K1riT0N/mobile-robot-competition/Reports/ROBOTIC COMPETITION REPORT.pdf

### KING MONGKUT’S INSTITUTE OF TECHNOLOGY LATKRABANG

### SCHOOL OF ENGINEERING

### ROBOTIC & AI ENGINEERING

### GROUP OF (RAI 1, RAI 2, HUACHIEW)

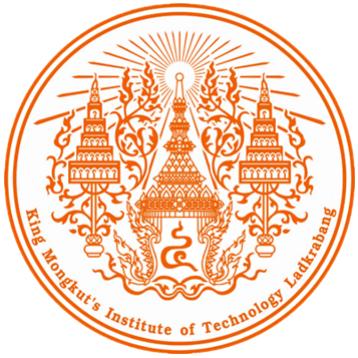
[picture p18: figure]

### ROBOTICS COMPETITION REPORT

INSTRUCTED BY: DR. POOM KONGHUAYROB

NAME: JAIJAI, NUUN, TITLE

GROUP NO: 03

DATE OF SUB.: 10/11/2568

### PURPOSE

- To practice coding for controlling real hardware such as motors, servos, and sensors.
- To create a function robots in both autonomous and manual control systems
- To develop 3D design and programming skill
- To apply physics principles to development and improvement of robotics systems for future innovation.

## AUTONOMOUS ROBOT

### COMPONENT LIST

- Arduino UNO
Parameter | Specification
microcontroller | ATmega328P
USB Controller | ATmega16U2
Operating Voltage | 5 V
Input Voltage | 7 - 12 V
Difital I/O Pins | 14 (6 PWM)
Communication | UART, I²C, SPI
Dimensions | 68.6 x 53.4 mm
Weight | 25 g

- TT DC Motor Dual-Shaft
Parameter | Specification
Gear Reduction Ratio | 1:48
Rated Voltage | 3 – 6 V
No-load Speed | ≈200 RPM at 6V
No-load Current | ≈150 mA at 6V
Stall Torque | ≈0.8 kg cm at 6V
Stall Current | ≈700 mA
Shaft Type | Double D-shaped output shaft
Gearbox Material | Plastic
Dimensions | ≈70 × 22 × 18 mm
Weight | ≈30 – 50 g
Power | ≈0.9 W
- SG90 Servo Motor 9g
Parameter | Specification
Operating Voltage | 4.8 - 6 V DC
Operating Current (No Load) | ~100 mA
Stall Current | ~680 mA
Torque | 1.8 kg cm at 4.8 V
Speed | 0.1 s/60° at 4.8 V
Rotation Angle | ~180°
Weight | 9 g

- Gyro Sensor MPU6050 GY-521
Parameter | Specification
Supply Voltage | 3 - 5 V DC
Gyro Range | ±250, ±500, ±1000, ±2000 °/s
Accelerometer Range | ±2g, ±4g, ±8g, ±16g
Operating Current | ~3.9 mA
Communication Speed | 400 kHz I²C
- L298N
Parameter | Specification
Motor Supply Voltage | 5 - 35 V DC
Logic Supply Voltage | 5 V
Continuous Output Current | 2 A per channel
Channels | 2 DC motors
Control Inputs | IN1, IN2, IN3, IN4
PWM Control | ENA, ENB
Peak Output Current | 3 A per channel
Thermal Shutdown | Build in

### ASSEMBLY DESIGN

### 1.1 Cube Collecting Mechanism

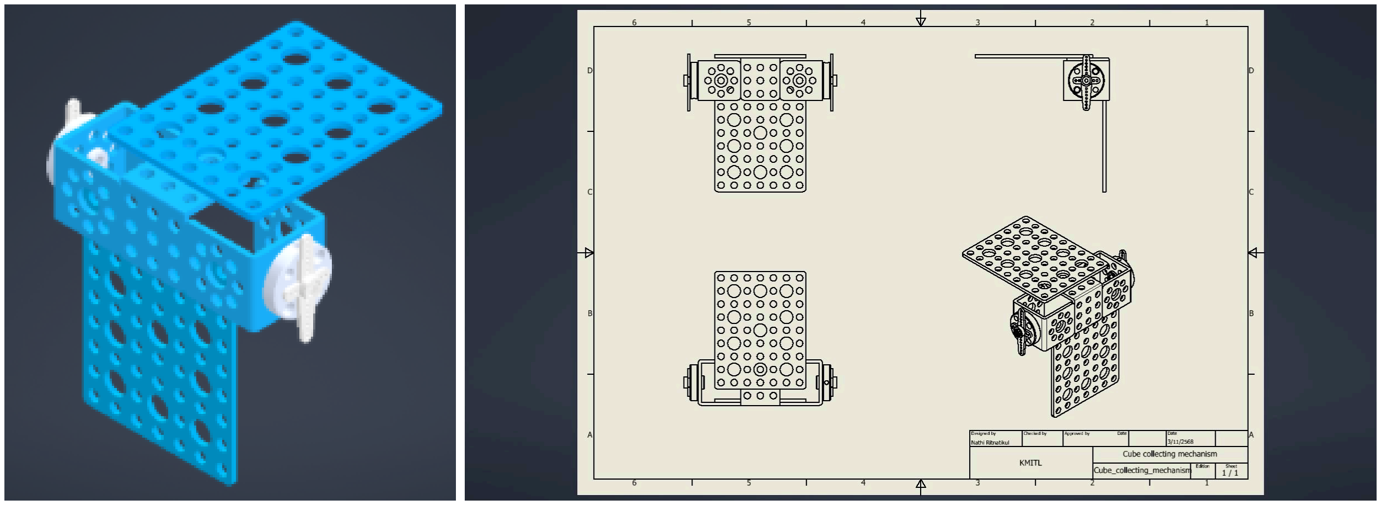
[picture p19: figure]
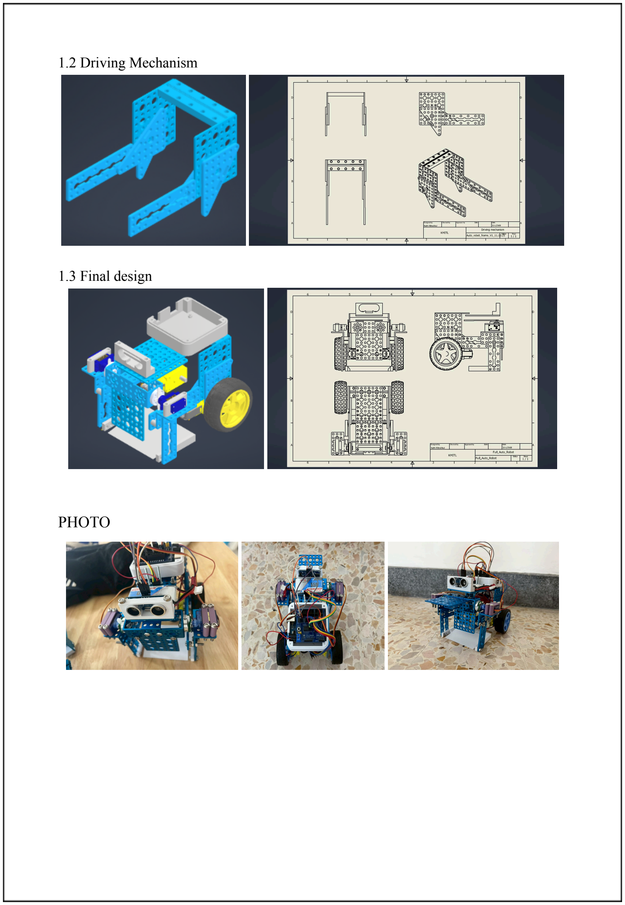
[picture p20: page 5]

### 1.2 Driving Mechanism

### 1.3 Final design

### PHOTO

### ELECTRICAL DIAGRAM

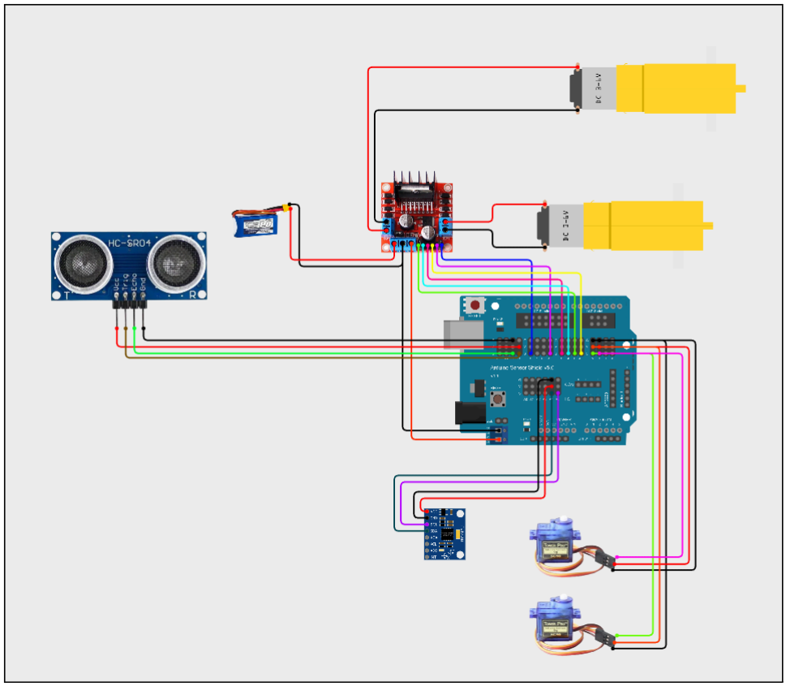
[picture p21: figure]

### CODING

- FLOWCHART

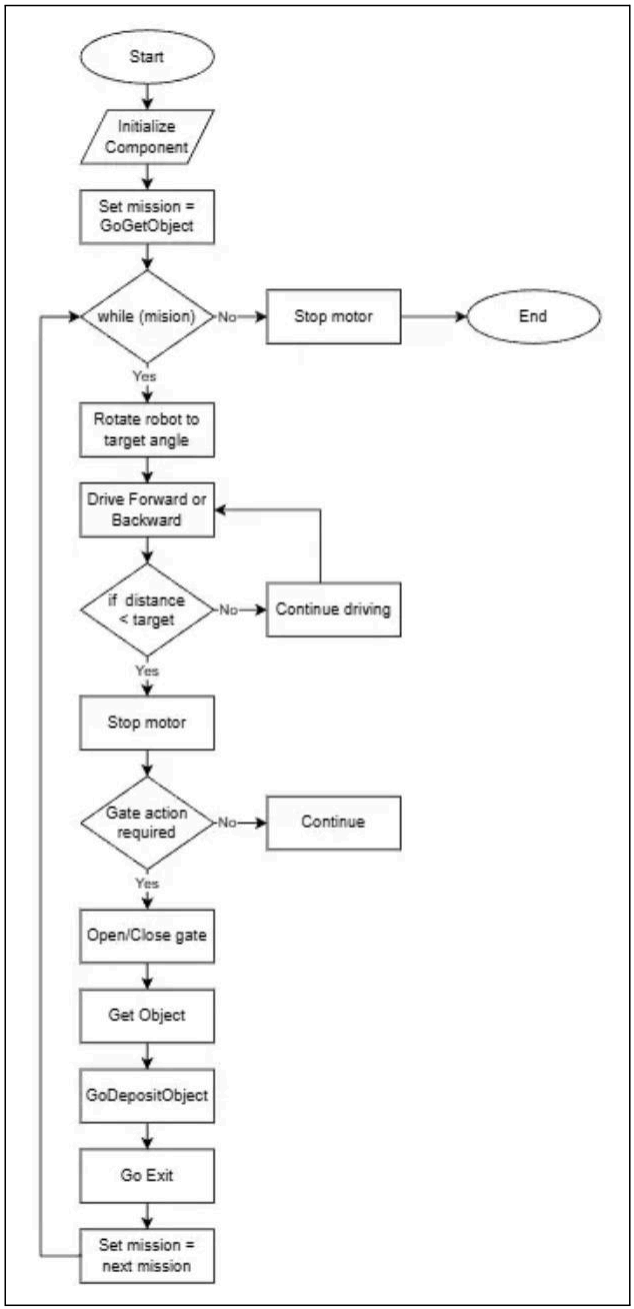
[picture p22: figure]

- FULL CODE AND EXPLANATION

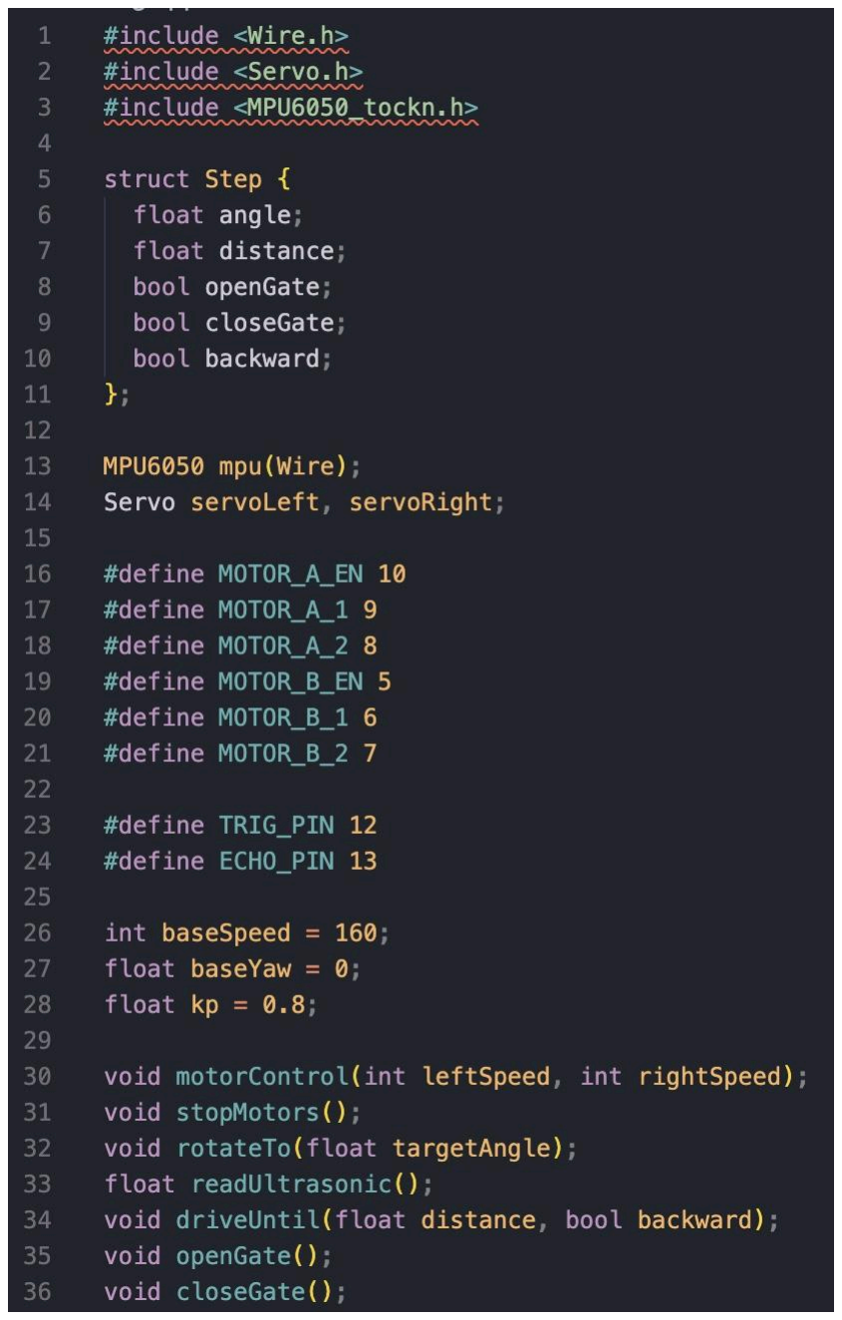
[picture p23: figure]

This part of the code sets up the fundamental structure, hardware definitions, and function declarations for an Arduino robot project that uses sensors and servos for motion and control. It begins by including three essential libraries: Wire.hfor I2C communication, Servo.h for controlling servo motors, and MPU6050_tockn.h for reading data from the MPU6050 gyro sensor. A custom structure named Step is then defined to store parameters for each robot movement, including turning angle, travel distance, and Boolean flags for actions such as openGate, closeGate, and backward. Next, objects for the MPU6050 sensor (mpu) and two servo motors (servoLeft and servoRight) are created. The motor pins for both left and right motors (MOTOR_A and MOTOR_B) are defined, along with the TRIG and ECHO pins used by the ultrasonic sensor for distance measurement. Several control constants are also initialized: baseSpeed (the normal motor speed), baseYaw (the initial orientation angle), and kp (the proportional control gain for rotation). Finally, a set of function prototypes is declared for key robot operations such as controlling motor speed, stopping, rotating to a specific angle, reading distance, driving a set distance, and opening or closing the servo-controlled gate which will be implemented later in the code.

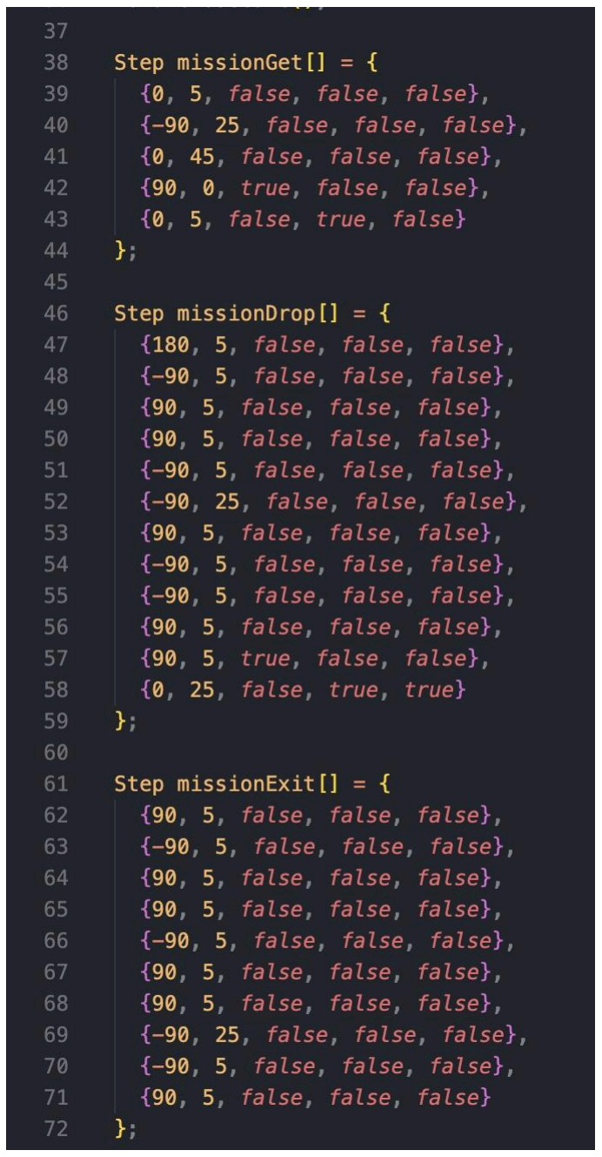
[picture p24: figure]

This section of the code defines three arrays — missionGet, missionDrop, and missionExit — each representing a different sequence of movement and action steps for the robot to perform during its operation. Each array is composed of elements based on the previously defined Step structure, where each step includes five parameters: the rotation angle, travel distance, and three Boolean flags (openGate, closeGate, backward) that specify additional actions.

missionGet describes the robot’s path for approaching and collecting an object. It includes commands to move forward, turn at specific angles (e.g., -90° or 90°), open the servo gate to collect the object, and then close it after pickup.

missionDrop outlines the robot’s path to transport and release the object. It involves multiple turns and straight movements to navigate toward the drop-off location, execute gate-opening actions to release the item, and finally close the gate while possibly reversing.

missionExit defines the route for the robot to leave the drop zone and return or exit the mission area, using a sequence of turns and short distance movements similar to the previous missions but without opening or closing the gate.

Overall, these structured arrays act as predefined mission plans, allowing the robot to follow step-by-step instructions autonomously without hardcoding movement logic inside the main loop.

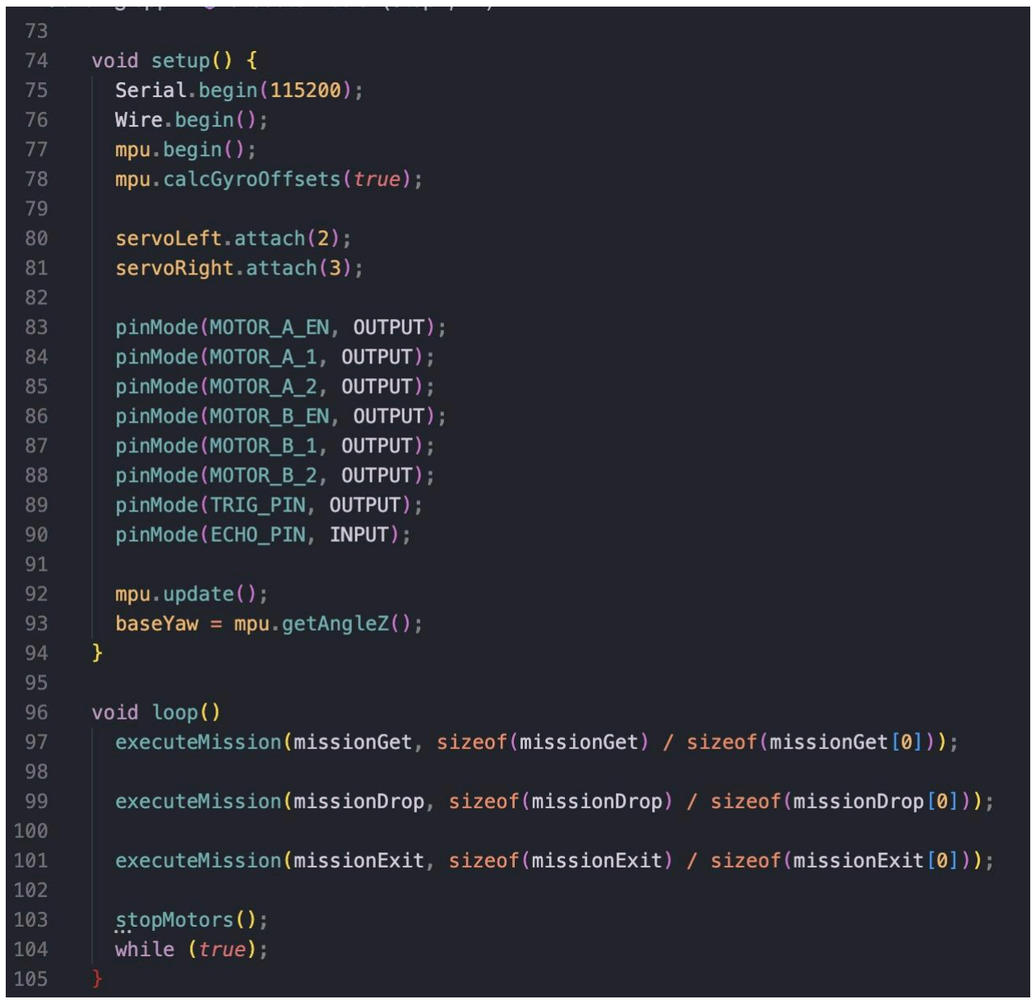
[picture p25: figure]

This part of the code initializes and defines the robot's main operational sequence. The setup() function is run once to prepare the hardware: it starts serial communication and I2C communication for sensors, initializes the MPU-6050 sensor (IMU) and calibrates its gyroscope, attaches the servo motors for mechanical actions, and sets the input/output roles for the DC motor control and ultrasonic sensor pins . It concludes by reading the initial heading from the MPU, storing it as baseYaw for navigation reference. The loop() function then runs the robot's complete mission by sequentially executing three defined phases: missionGet, missionDrop, and missionExit. After completing all three missions, it calls stopMotors() to disable movement and enters an infinite while(true) loop, effectively ending the robot's active program execution.

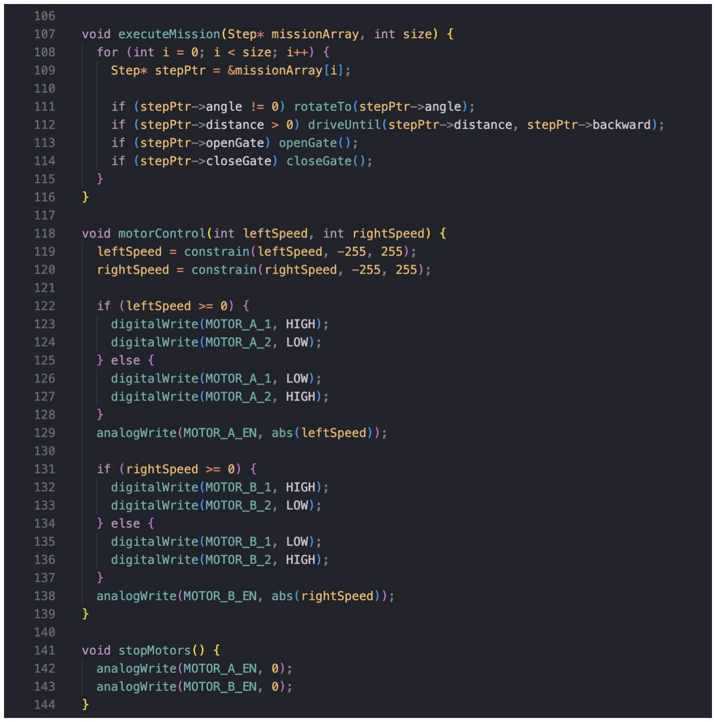
[picture p26: figure]

This segment of code contains the core motion and mission control logic for the robot. The executeMission() function is responsible for iterating through an array of mission steps and calling the appropriate action functions based on the step's data (angle, distance, openGate, or closeGate). The motorControl() function manages the speed and direction of the drive motors: it first ensures the input leftSpeed and rightSpeed values are within the acceptable range (-255 to 255) using constrain(); it then uses digitalWrite() on pins MOTOR_A_1/2 and MOTOR_B_1/2 to set the direction(forward or backward) and employs analogWrite() on the enable pins (MOTOR_A_EN and MOTOR_B_EN) with the absolute speed value to set the motor's velocity using PWM. Finally, the simple stopMotors() function immediately halts both motors by setting the PWM signal on their enable pins to 0.

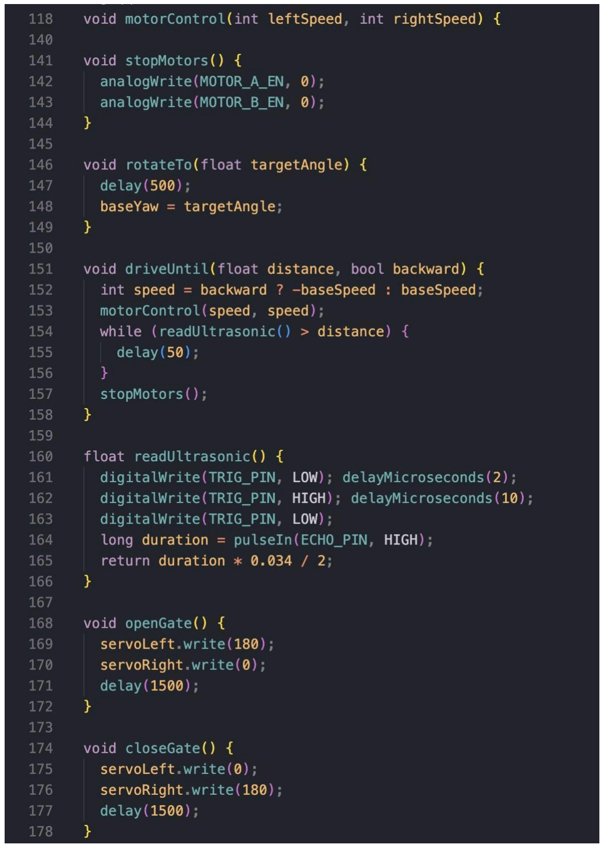
[picture p27: figure]

This section contains the specialized movement and sensing functions of the robot. The readUltrasonic() function measures distance by sending a brief pulse from the TRIG_PIN, waiting for the return echo on the ECHO_PIN , and converting the sound wave's travel time into centimeters. The driveUntil() function moves the robot forward or backward at a defined base speed using motorControl() and continuously checks the distance from the ultrasonic sensor; it stops the motors once the remaining distance is less than the target distance. The rotateTo() function simply sets a new baseYaw reference angle for navigation after a short pause. Lastly, the openGate() and closeGate() functions control the robot's mechanical action by commanding the two servo motors to move to their respective extreme angles (0 or 180 degrees) and pausing briefly to allow the action to complete.

### CODE Explanation

The objective of this project is to design and implement an Arduino-controlled robot that can autonomously navigate a predefined path, perform object collection and drop-off tasks, and finally return to the exit.

The robot uses an ultrasonic distance sensor to detect obstacles, servo motors to operate a gate mechanism, and DC motors to move and rotate according to programmed instructions. At first we were planning on using gyro (MPU6050) but the coding part doesn't work so we use other methods to code without gyro instead.

- Functions : for organized, reusable code blocks.
- Structure (struct) : to store mission step data such as angle, distance, and gate action.
- Array : to hold multiple mission steps for each phase of the route.
- Pointer : to iterate and access mission step data dynamically.
- Loops : to repeatedly execute mission sequences automatically.

Explanation of Main Components

A structure named MissionStep is declared to store

- targetAngle : defines how much the robot should rotate before moving forward
- distance : defines the forward movement distance in centimeters measured by the ultrasonic sensor.
- gateAction : determines whether to open or close the servo gate during that step.

This makes it easy to represent every movement and action as one simple, structured dataobject.

Array and Pointer

The program defines three separate arrays to represent the route phases:

1. getObject[] → path for collecting the object
2. dropObject[] → path for delivering the object
3. exitPath[] → path to return to the exit

Each array contains multiple MissionStep elements describing angles, distances, and gate actions.

A pointer MissionStep* missionPtr is used to access the array dynamically during loop execution:

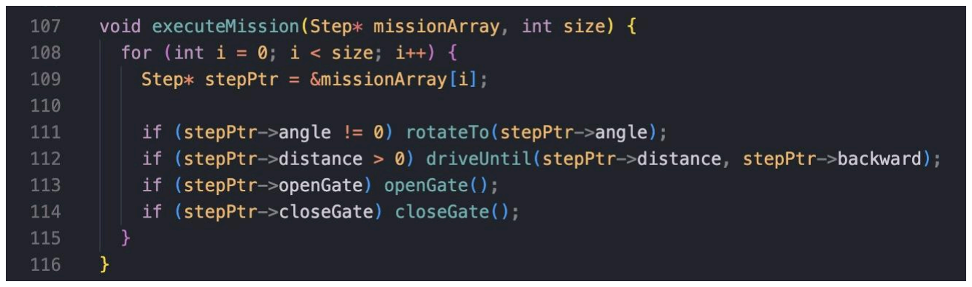
[picture p28: figure]

This loop executes:

Rotation : robot turns to target angle.

Forward movement : continues until ultrasonic sensor reads the specified distance.

Gate control : opens/closes if gateAction = true.

Using for loops reduces code repetition and enables multiple mission sequences to run automatically.

Functions
setupMotors() : Initializes motor driver pins.
driveStraight(int speed) : Moves robot forward at given speed. stopMotors() : Stops both motors.
readUltrasonic() : Reads distance in cm using the ultrasonic sensor. rotateTo(float targetAngle): Simulates rotation to a desired angle. openGate() / closeGate(): Controls servo motors for gate mechanism.

## Control Flow Explanation (Logic)

### Go Get Object

- Robot starts moving forward until the ultrasonic sensor detects an object at 5 cm.
- Turns left 90° and continues 25 cm forward.
- Turns right 90°, moves 45 cm, then right 90° again.
- At this position, the robot opens the gate to collect the object.
- Moves forward 5 cm, then closes the gate.

### Go Drop Object

- Robot turns 180°, retraces its path through a sequence of left and right turns and forward moves (5–25 cm each).
- After reaching the drop location, the robot opens the gate to release the object.
- Moves backward 25 cm, then closes the gate to prepare for exit.

### Go to EXIT

- The robot follows a complex navigation path using multiple 90° turns and 5 cm forward moves.
- Finally stops when it reaches the final exit point, completing the mission.
- Each phase is represented as a series of MissionSteps processed in sequence by the same loop logic — demonstrating modular programming and structural reusability.

## Sensor and Actuator Coordination

The ultrasonic sensor (using TRIG and ECHO pins) constantly measures distance using sound wave reflection.
It controls when the robot should stop moving forward.

The servo motors attached to the gate act as the mechanical arm for grabbing or releasing the object.

DC motors are used for driving and turning, controlled by PWM signals (analogWrite()).

## MANUAL ROBOT

### COMPONENT LIST

- 180 Optical Encoder Motor
Parameter | Specification
Rated voltage | 7.4 V
Gear reduction ratio | 39.6 : 1
No-load current | 240 mA
Load current | ≤ 750 mA
No-load speed | 350 ± 5% RPM
Original motor speed | 14,000 ± 5% RPM
Start torque | 5 kg cm
Rated torque | 0.8 kg cm
Output shaft length | 9 mm
Power | 3.7 W
Encoder rotation angle | 360°
Motor type | DC motor with encoder
Control method | PWM or closed-loop feedback via encoder
- MS-1.5A Servo
Parameter | 4.6 V | 6.0 V | Unit | Tolerance
Running speed (no load) | 0.11 s/60° | 0.10 s/60° | s/60° | ±0.01 s
Operating current (no load) | 270 mA | 380 mA | mA | ±50 mA
Stall torque (locked) | 1.5 kg·cm | 1.8 kg·cm | kg·cm | ±0.30 kg·cm
Stall current (locked) | 1200 mA | 1500 mA | mA | ±50–70 mA
Idle current (when stopped) | 4 mA | 4 mA | mA | ±1 mA
Service life (no load) | >180,000 cycles | >150,000 cycles | cycles | –

- Digital Servo MEDS15
Parameter | Specification
Operating voltage range | 4.8 V to 6.8 V
No-load idle current | 4-5 mA
No-load speed | 62 - 71 RPM (at 6.8V)
Stall torque | 18 - 21.5 kg cm (at 6.8V)
Stall current | 1.5 - 2.2 A (at 5 - 6.8V)
Control signal | PWM (pulse-width modulated)
Rotation Range | 180°
- TT DC Motor Single-Shaft
Parameter | Specification
Gear Reduction Ratio | 1:48
Rated Voltage | 3 – 6 V
No-load Speed | ≈200 RPM at 6V
No-load Current | ≈150 mA at 6V
Stall Torque | ≈0.8 kg cm at 6V
Stall Current | ≈700 mA
Shaft Type | Single D-shaped output shaft
Gearbox Material | Plastic
Dimensions | ≈70 × 22 × 18 mm
Weight | ≈30 – 50 g
Power | ≈0.9 W

- mBot2 Shield
Component | Specification
Main Controller | CyberPi
Processor | ESP32-WROVER-B Dual-Core
Memory | 8 MB Flash, 8 MB PSRAM
Display | 1.44-inch Full-Color TFT
Communication | Wi-Fi 2.4GHz / Bluetooth 5.0
Interface Ports | 1×USB-C, 1×mBuild Port, 1×Extension Port
Power Supply | 3.7V Li-ion Battery (2500 mAh typical)
Operating Voltage | 3.3V Logic Level
Programming | mBlock 5 / Python / Arduino Mode
- Bluetooth Controller
Parameter | Specification
Material | ABS
Bluetooth Version | 4.0
Trasmission Distance | 20 m
Power supply | 5AA batteries

### ASSEMBLY DESIGN

### 1.1 Version 1

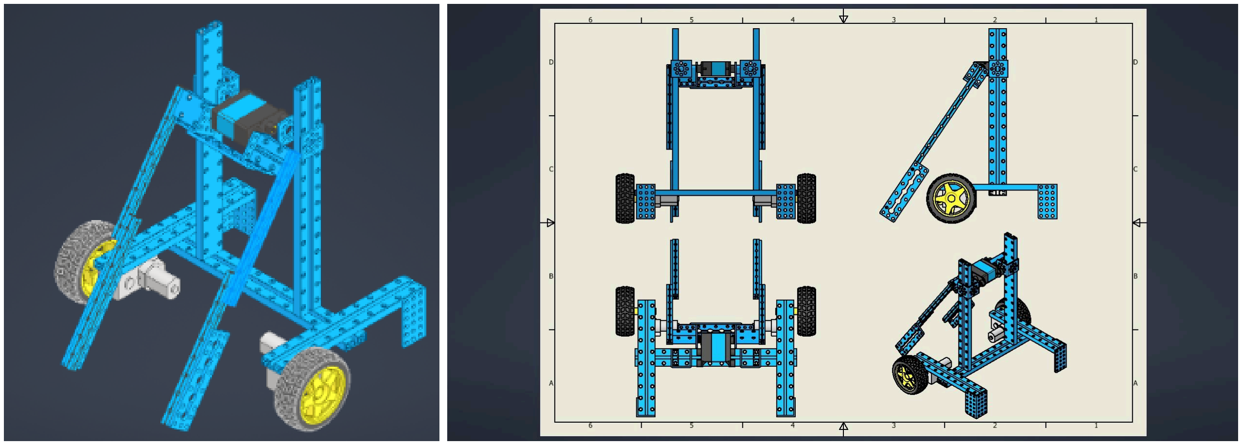
[picture p29: figure]
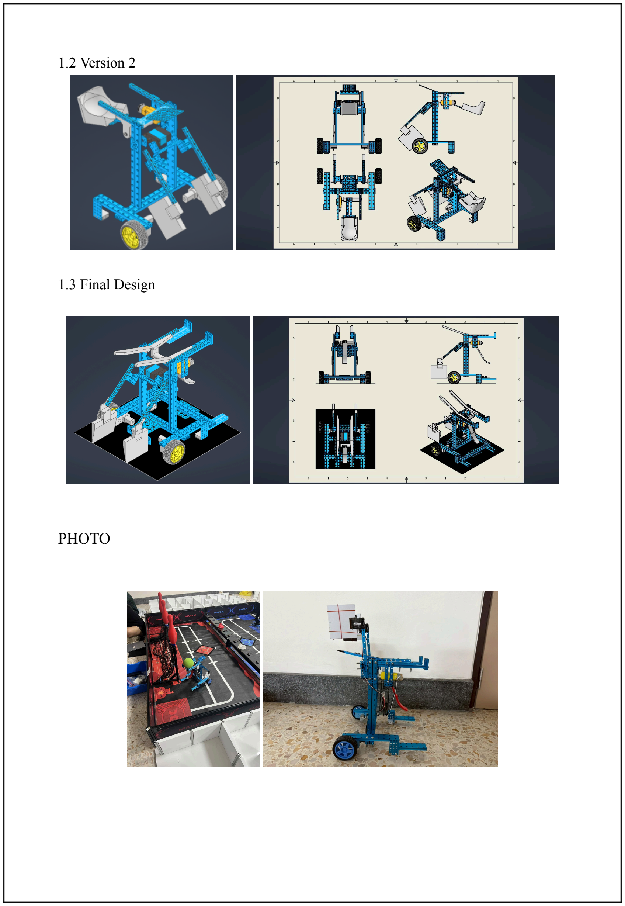
[picture p30: page 19]

### 1.2 Version 2

### 1.3 Final Design

### PHOTO

### ELECTRICAL DIAGRAM

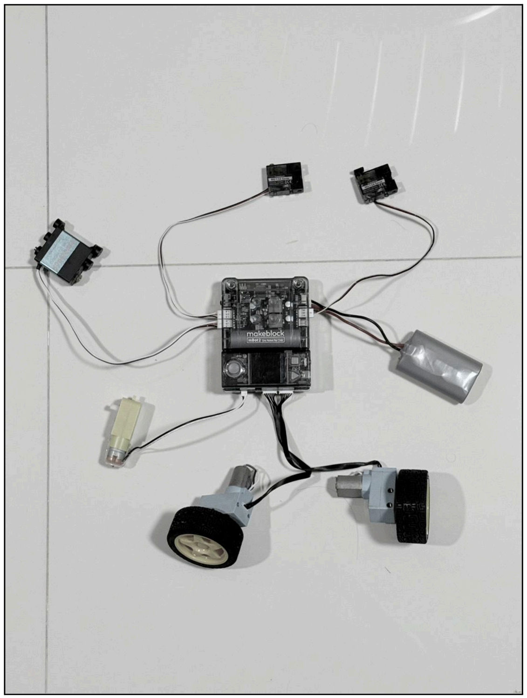
[picture p31: figure]

### CODING

- FLOWCHART

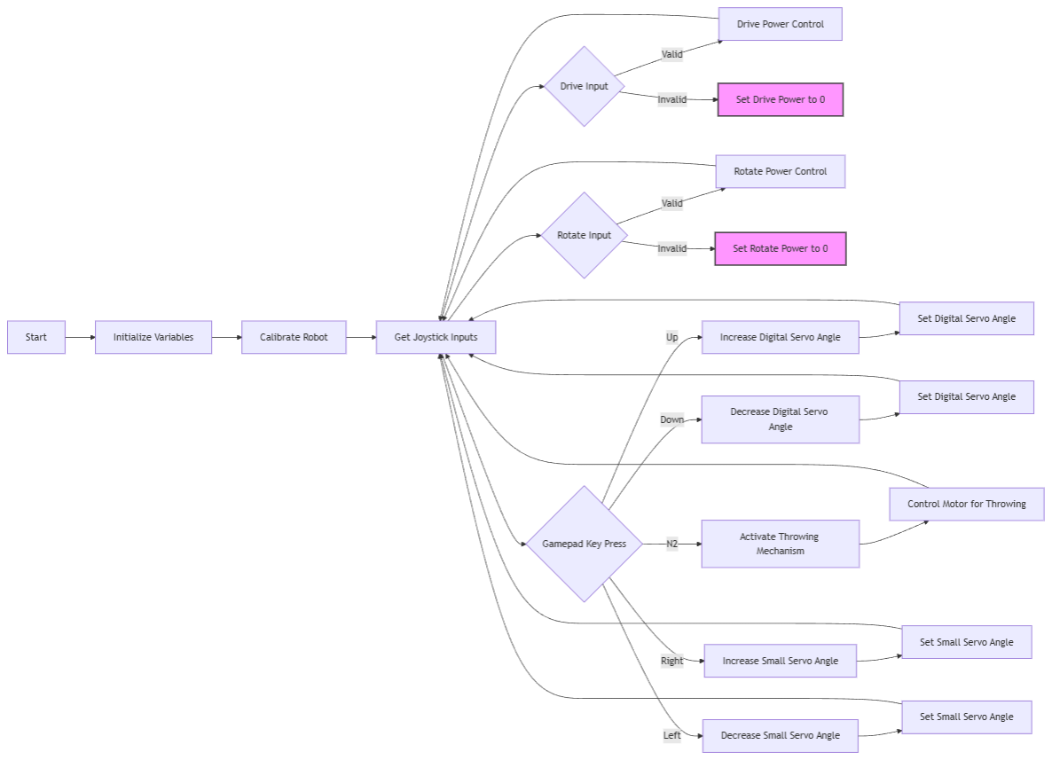
[picture p32: figure]
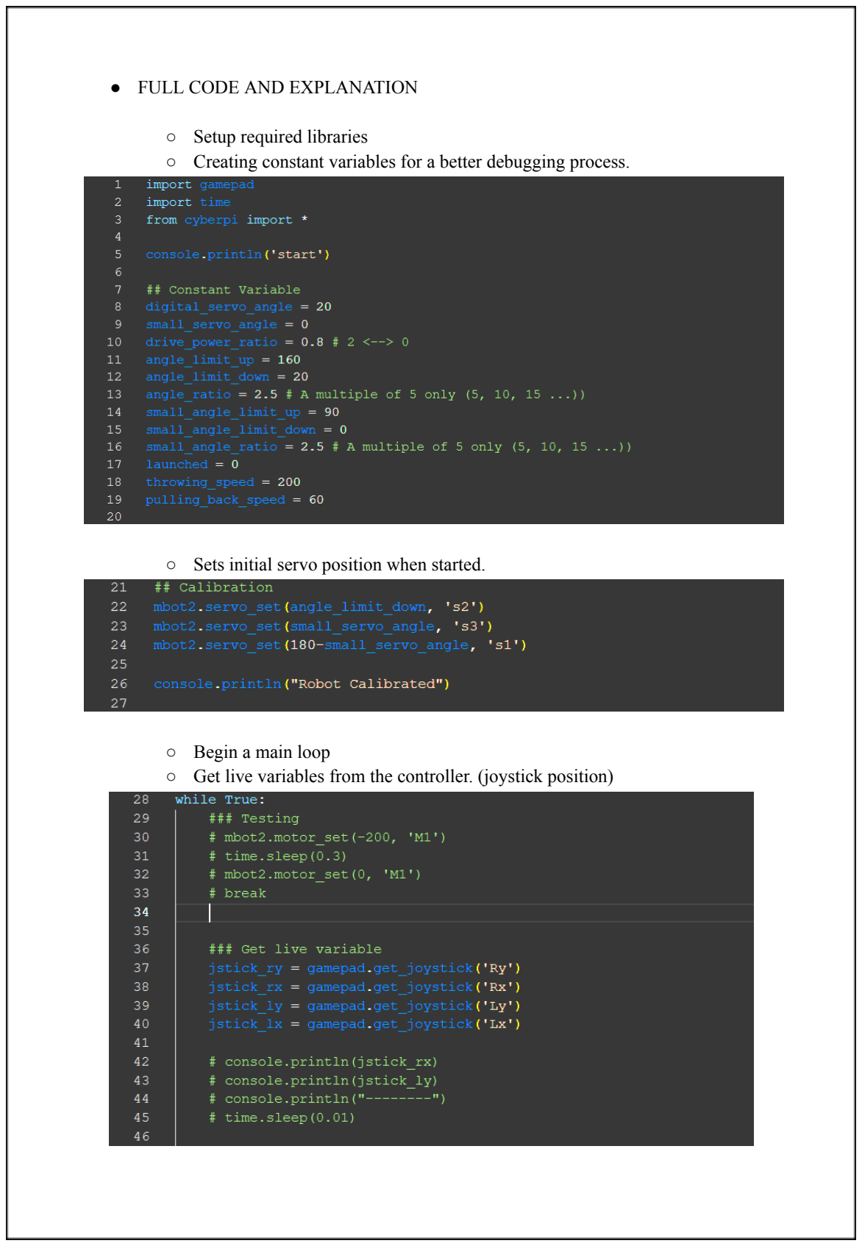
[picture p33: page 22]

- FULL CODE AND EXPLANATION
- Setup required libraries
- Creating constant variables for a better debugging process.
- Sets initial servo position when started.
- Begin a main loop
- Get live variables from the controller. (joystick position)

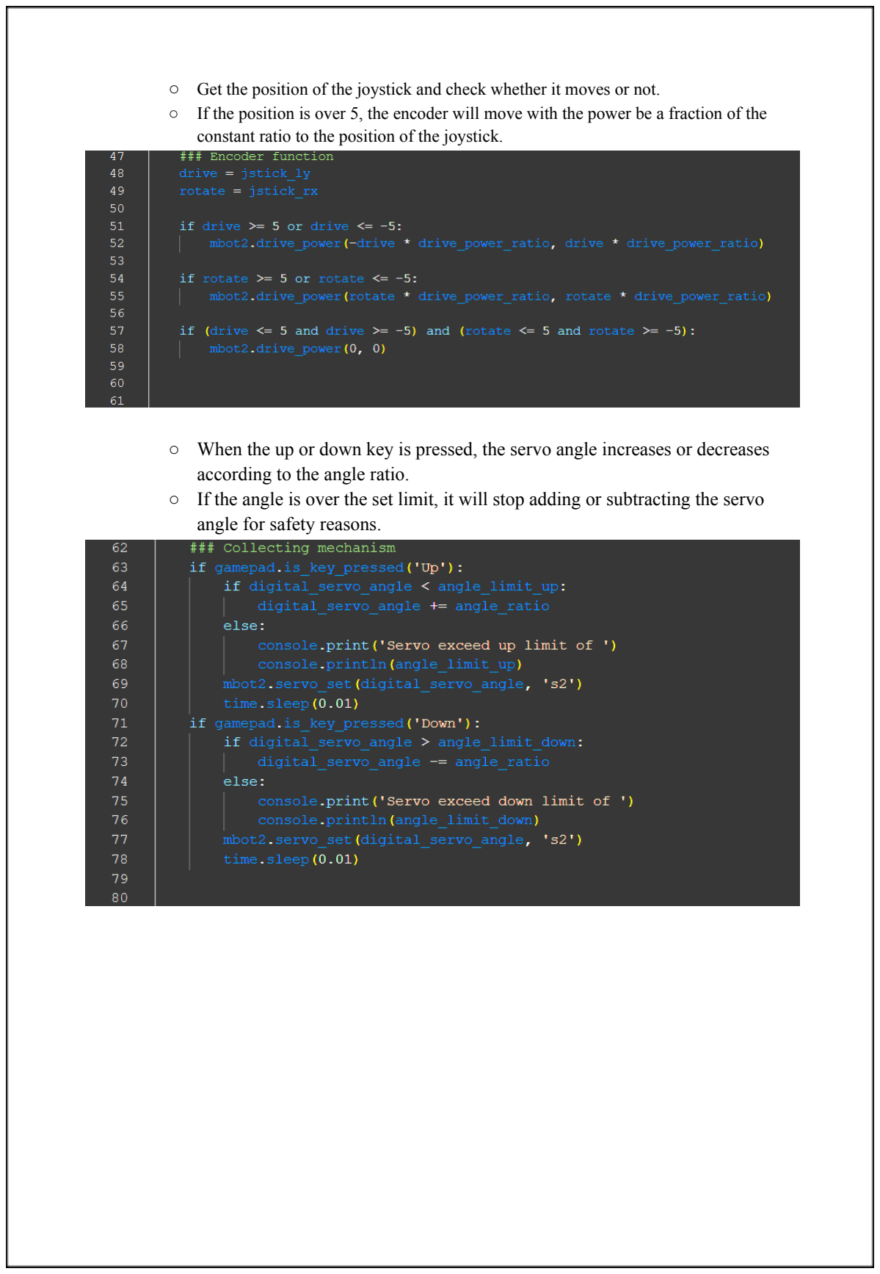
[picture p34: page 23]

- Get the position of the joystick and check whether it moves or not.
- If the position is over 5, the encoder will move with the power be a fraction of the constant ratio to the position of the joystick.
- When the up or down key is pressed, the servo angle increases or decreases according to the angle ratio.
- If the angle is over the set limit, it will stop adding or subtracting the servo angle for safety reasons.

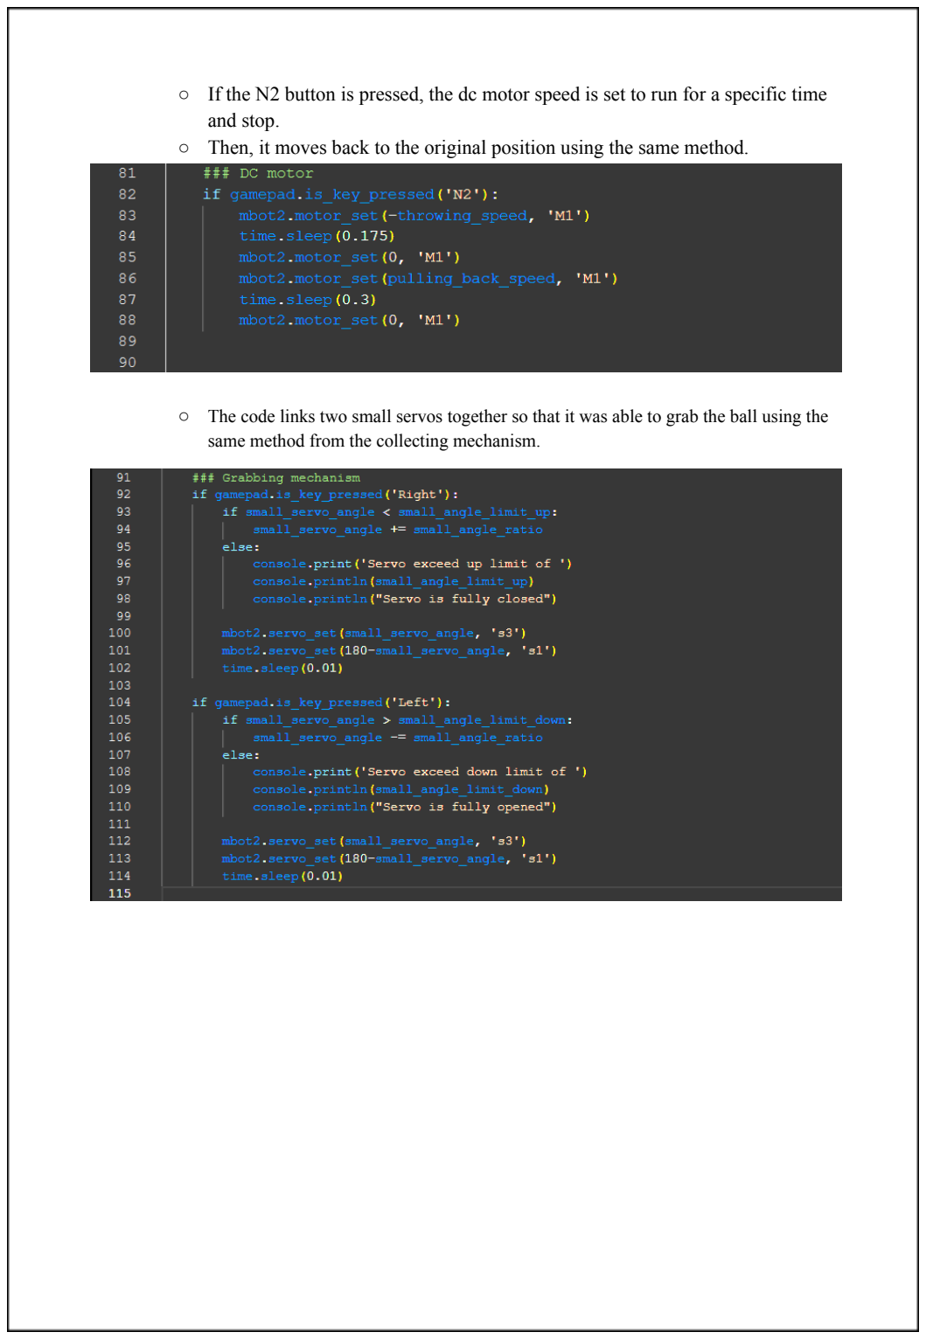
[picture p35: page 24]

- If the N2 button is pressed, the dc motor speed is set to run for a specific time and stop.
- Then, it moves back to the original position using the same method.
- The code links two small servos together so that it was able to grab the ball using the same method from the collecting mechanism.

## Group Evaluation

NAME | CONTRIBUTION | EVALUATED BY | CONFIRM BY
Nathi Ritnatikul | 100%
Kullatida Raksanaves | 100%
Thannapat Ketbunchoo | 100%
